petru-florea/Low-Frequency-Amplifier/Simulations/1.PNG

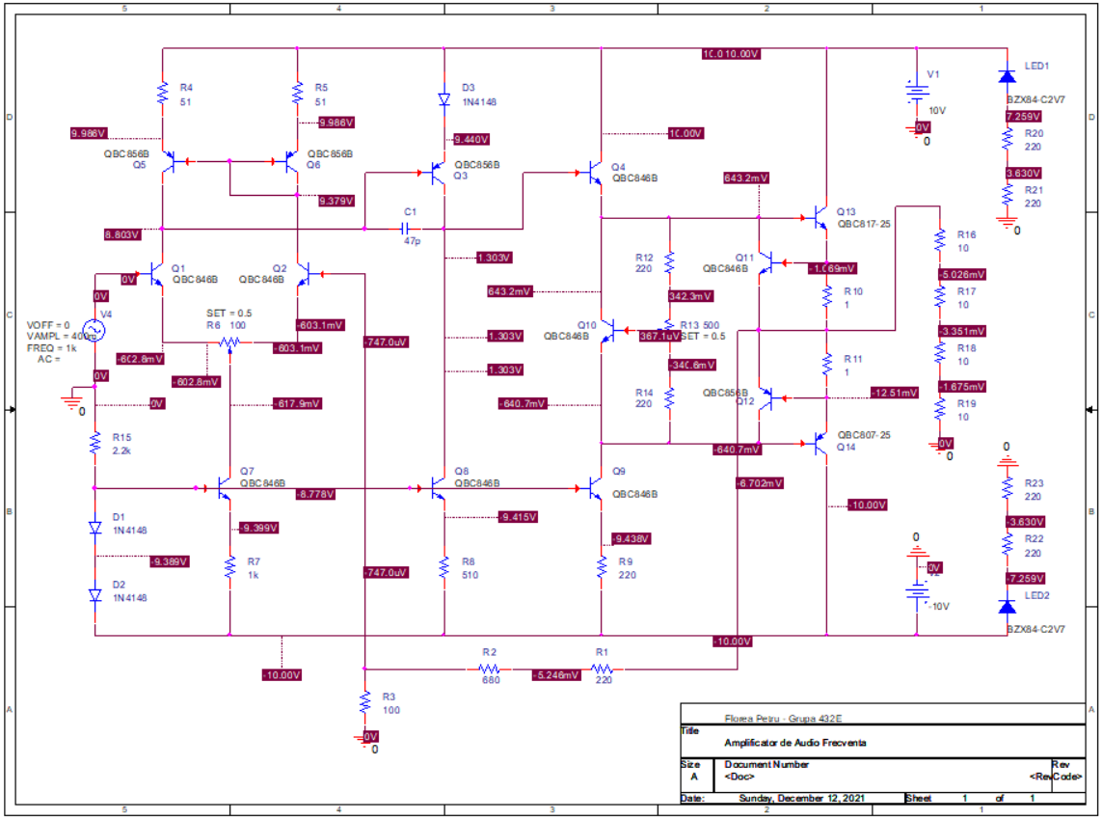
Simulations/1.PNG
