petru-florea/Low-Frequency-Amplifier/Simulations/2.PNG

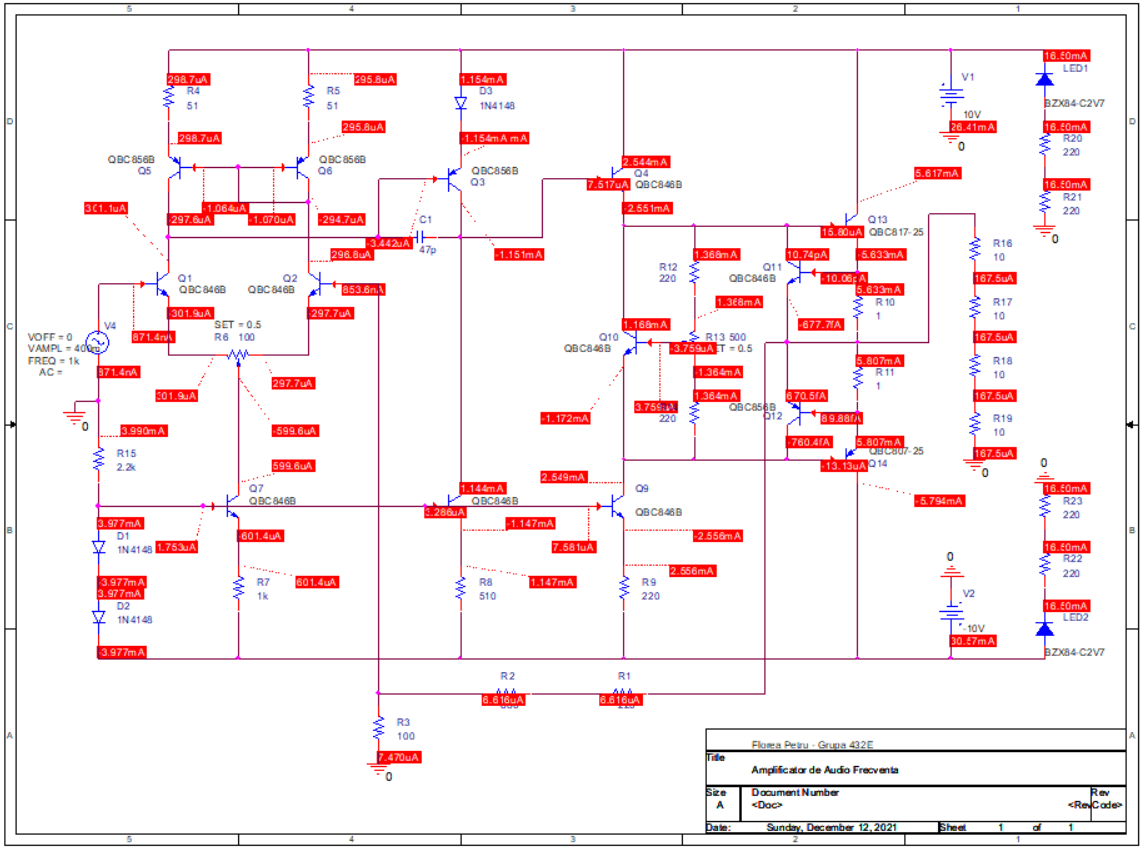
Simulations/2.PNG
