petru-florea/Low-Frequency-Amplifier/Simulations/3.PNG

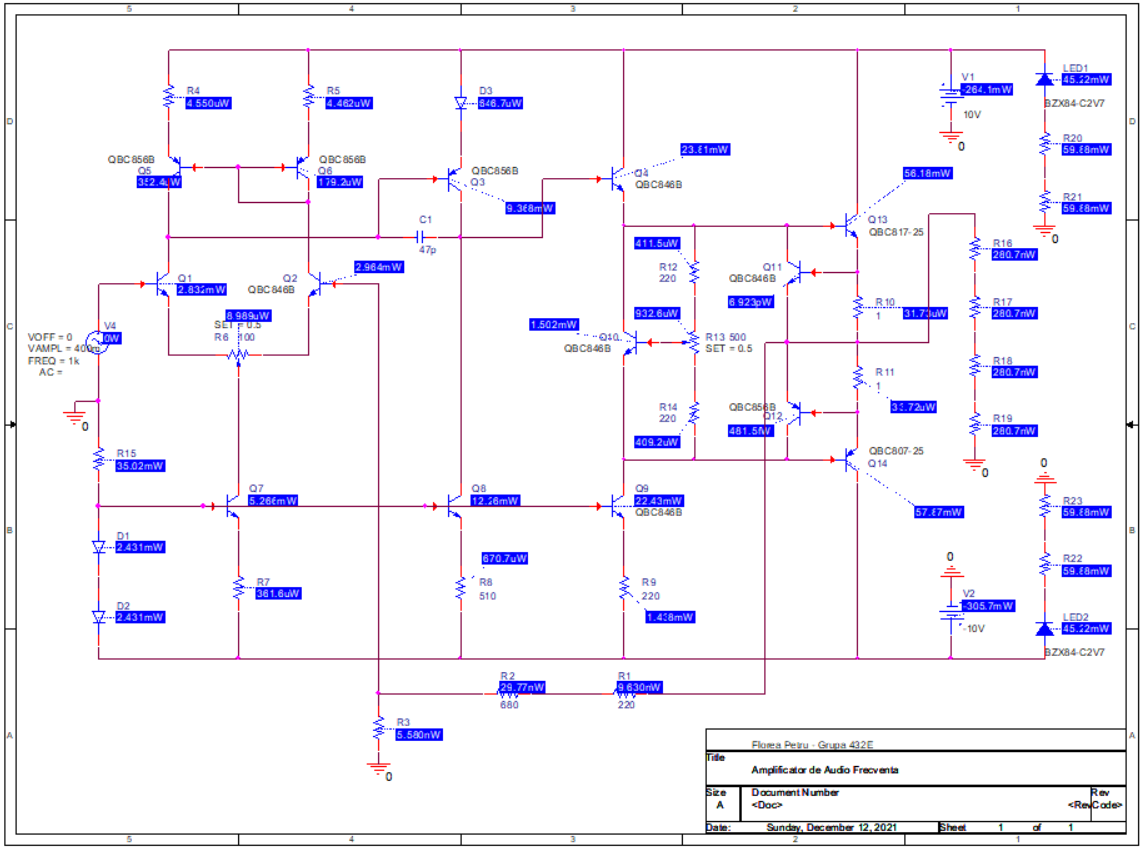
Simulations/3.PNG
