petru-florea/Low-Frequency-Amplifier/Simulations/4.JPG

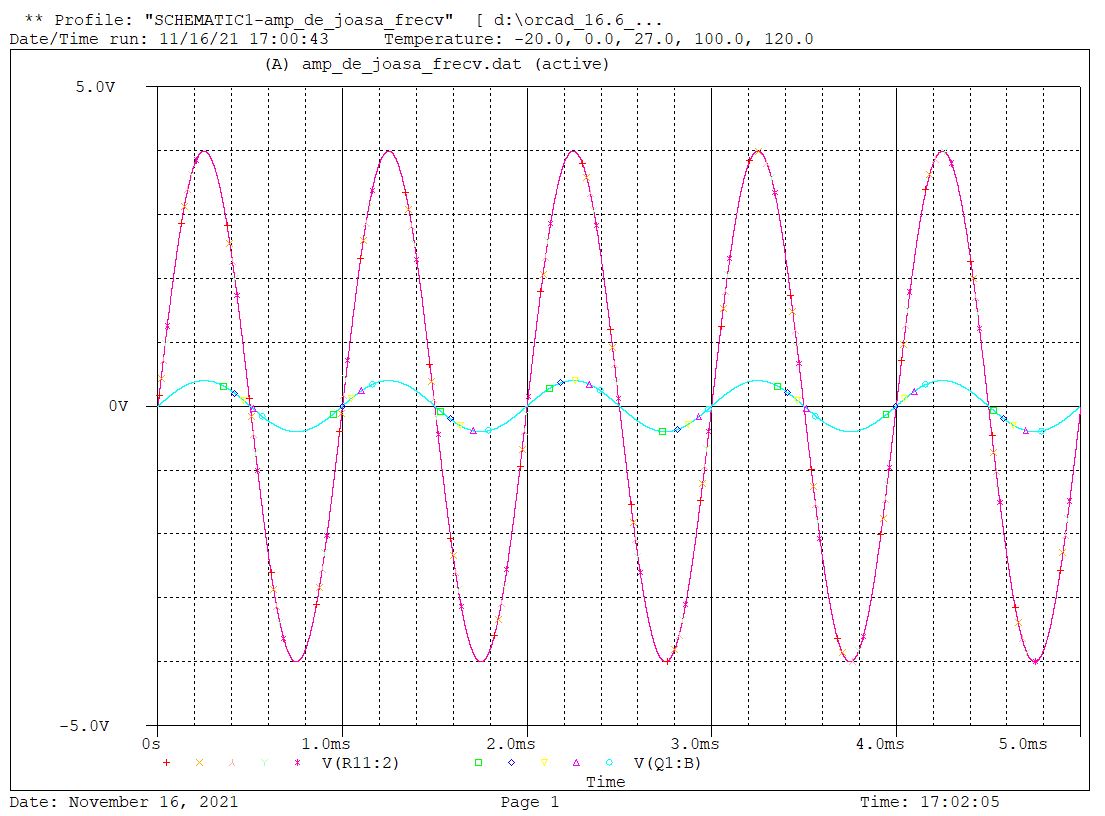
Simulations/4.JPG
