petru-florea/Low-Frequency-Amplifier/Simulations/5.JPG

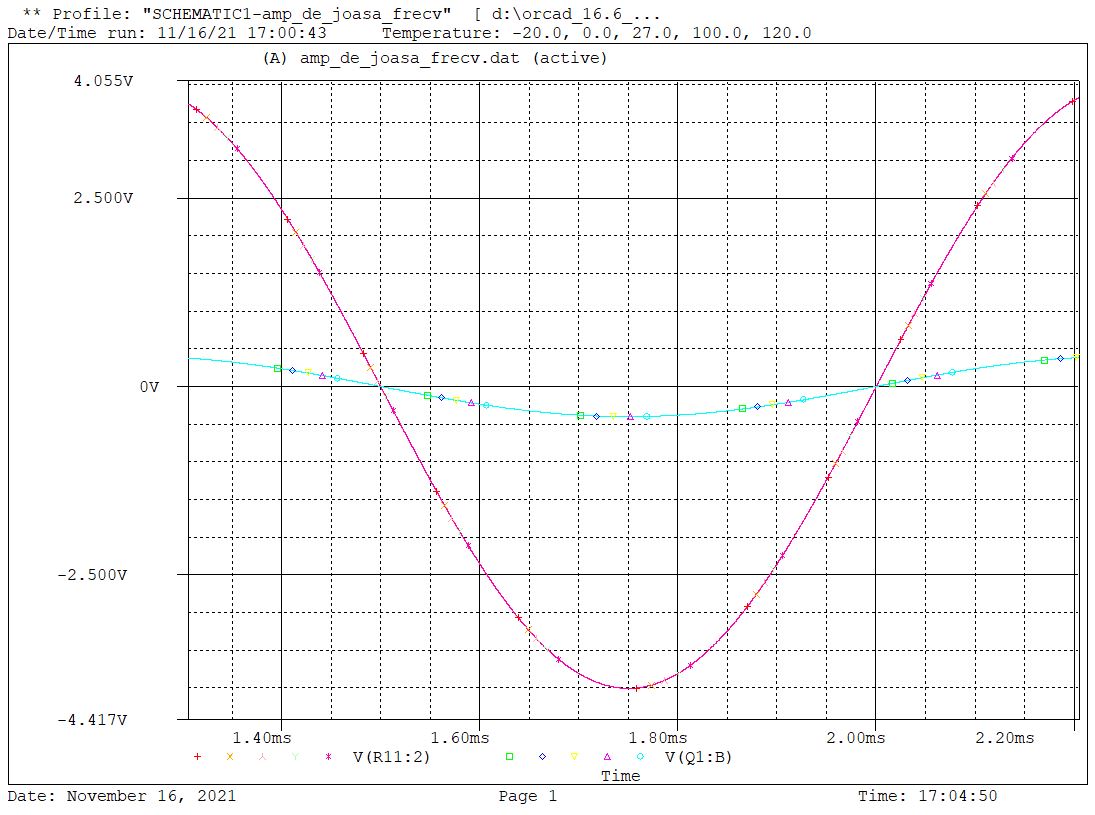
Simulations/5.JPG
