petru-florea/Low-Frequency-Amplifier/Simulations/6.JPG

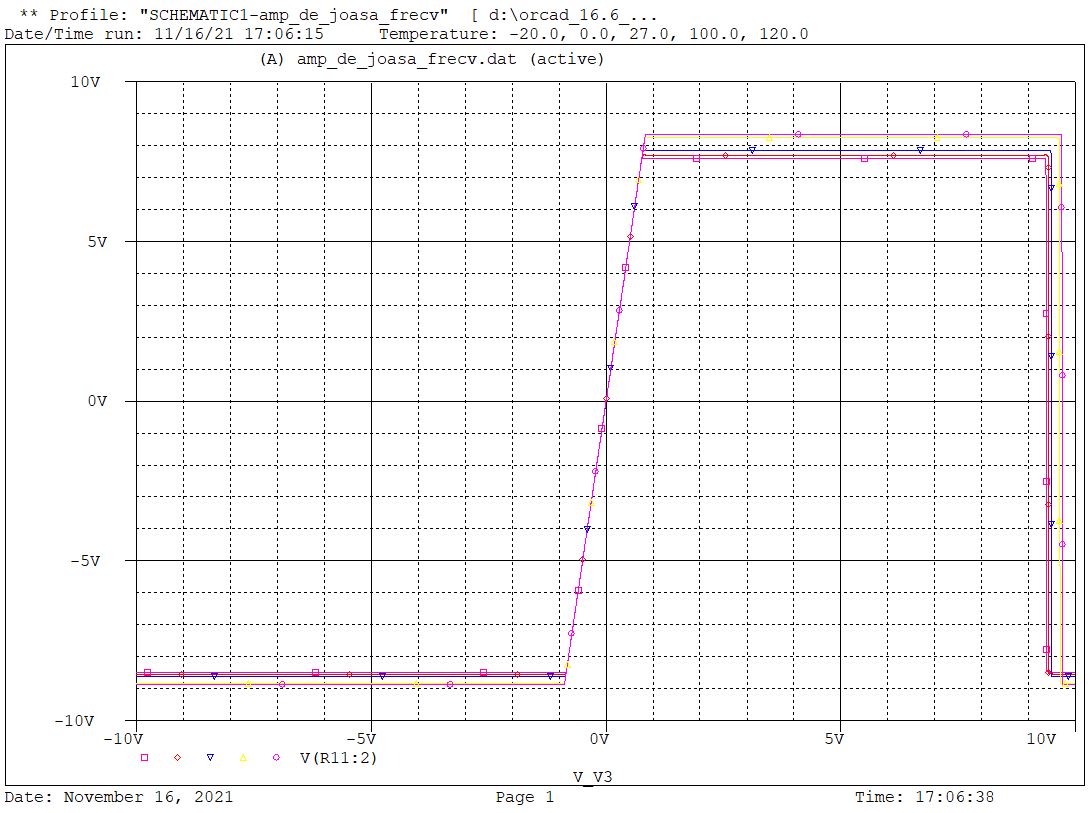
Simulations/6.JPG
