petru-florea/Low-Frequency-Amplifier/Simulations/7.JPG

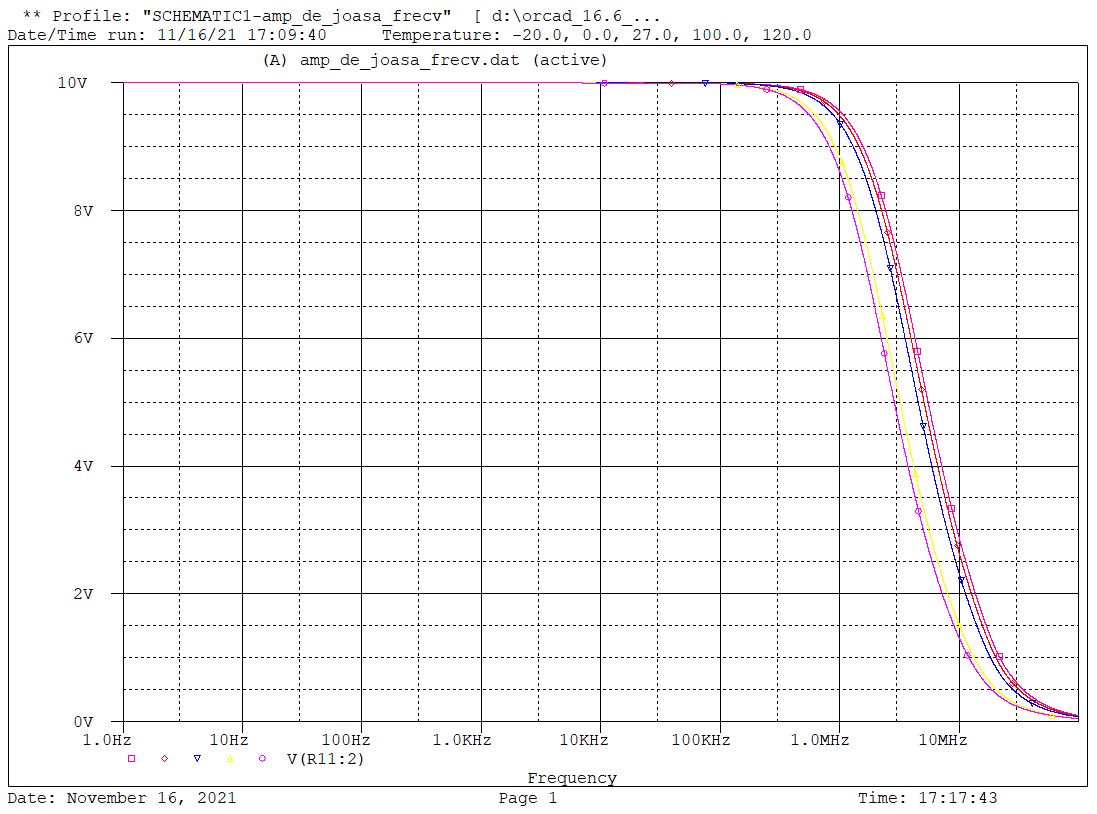
Simulations/7.JPG
