petru-florea/Low-Frequency-Amplifier/Simulations/8.JPG

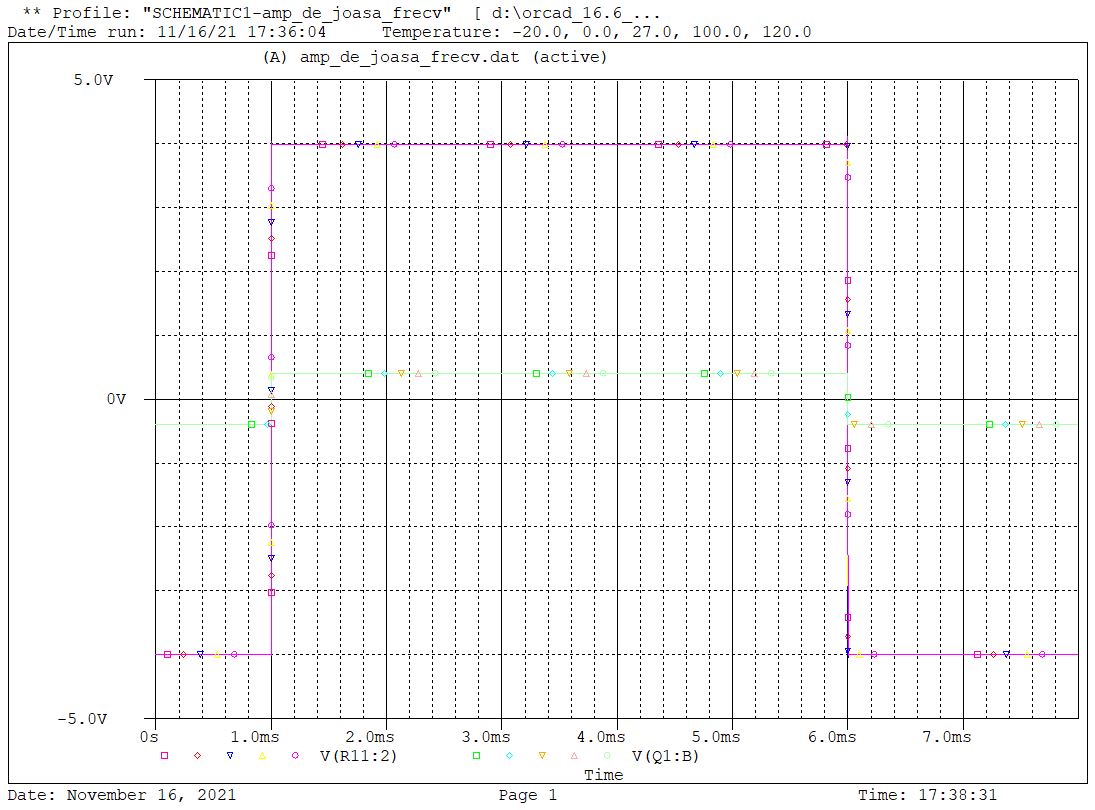
Simulations/8.JPG
