petru-florea/Low-Frequency-Amplifier/Simulations/9.JPG

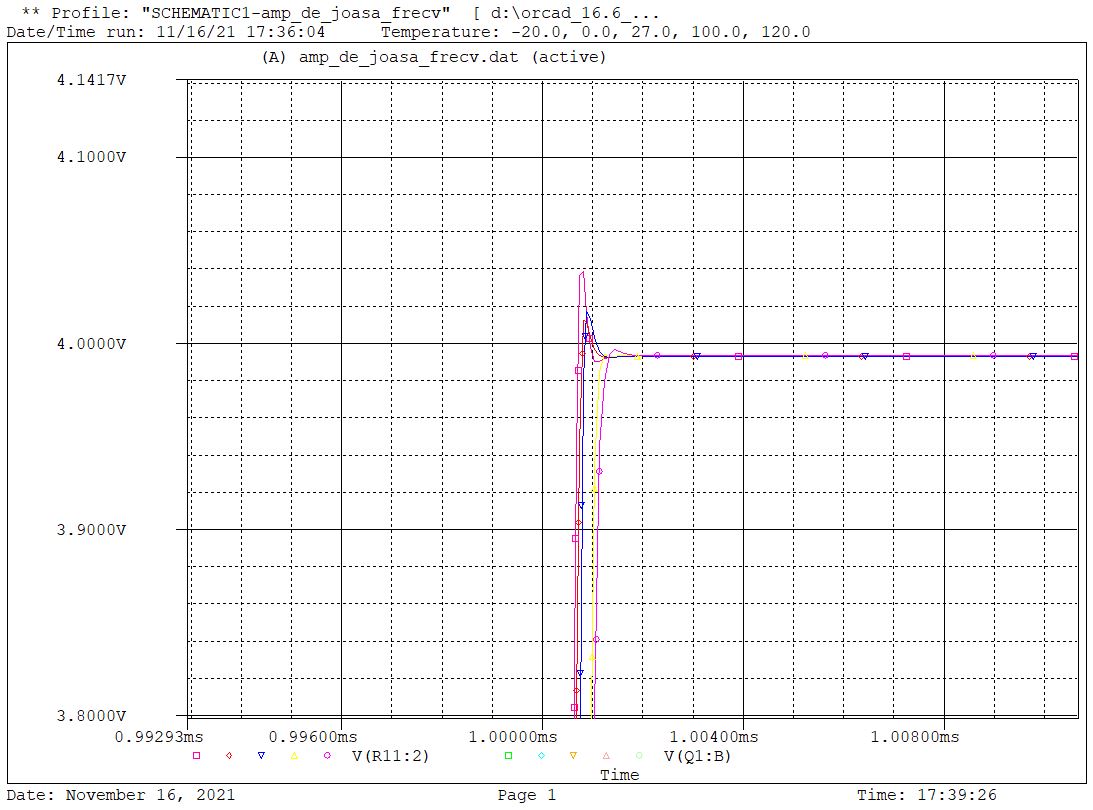
Simulations/9.JPG
