petru-florea/Low-Frequency-Amplifier/Simulations/10.JPG

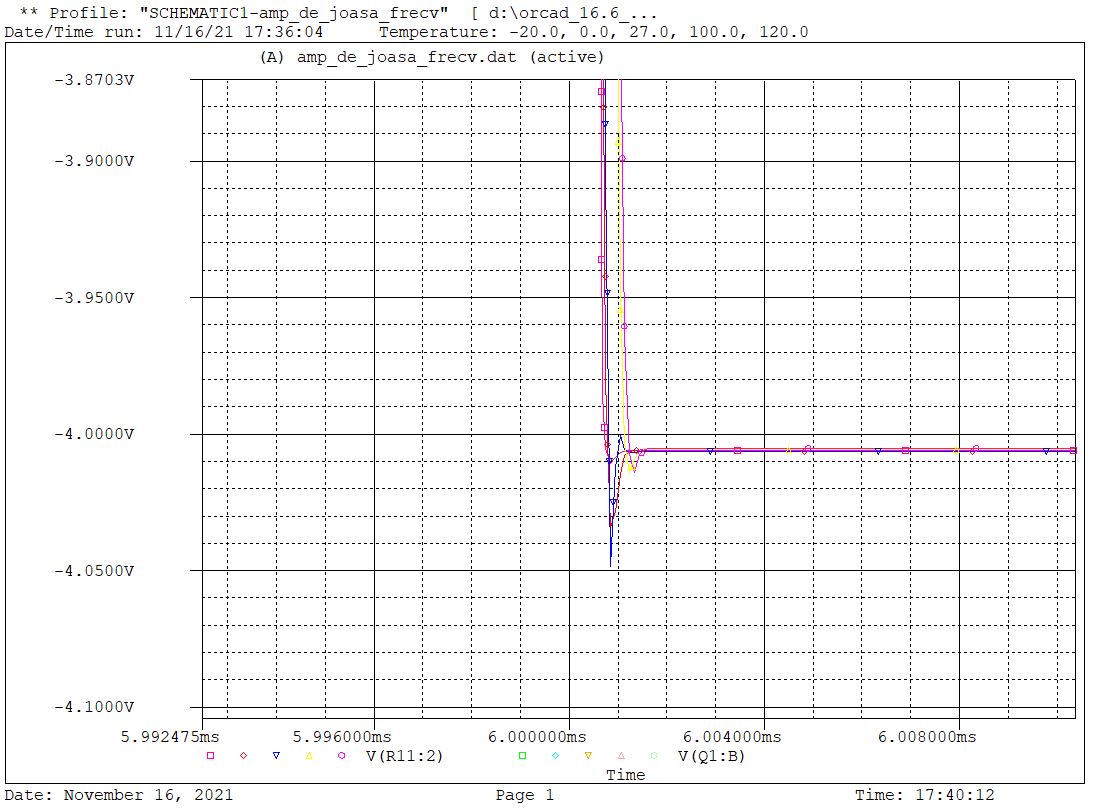
Simulations/10.JPG
