petru-florea/Low-Frequency-Amplifier/Simulations/11.JPG

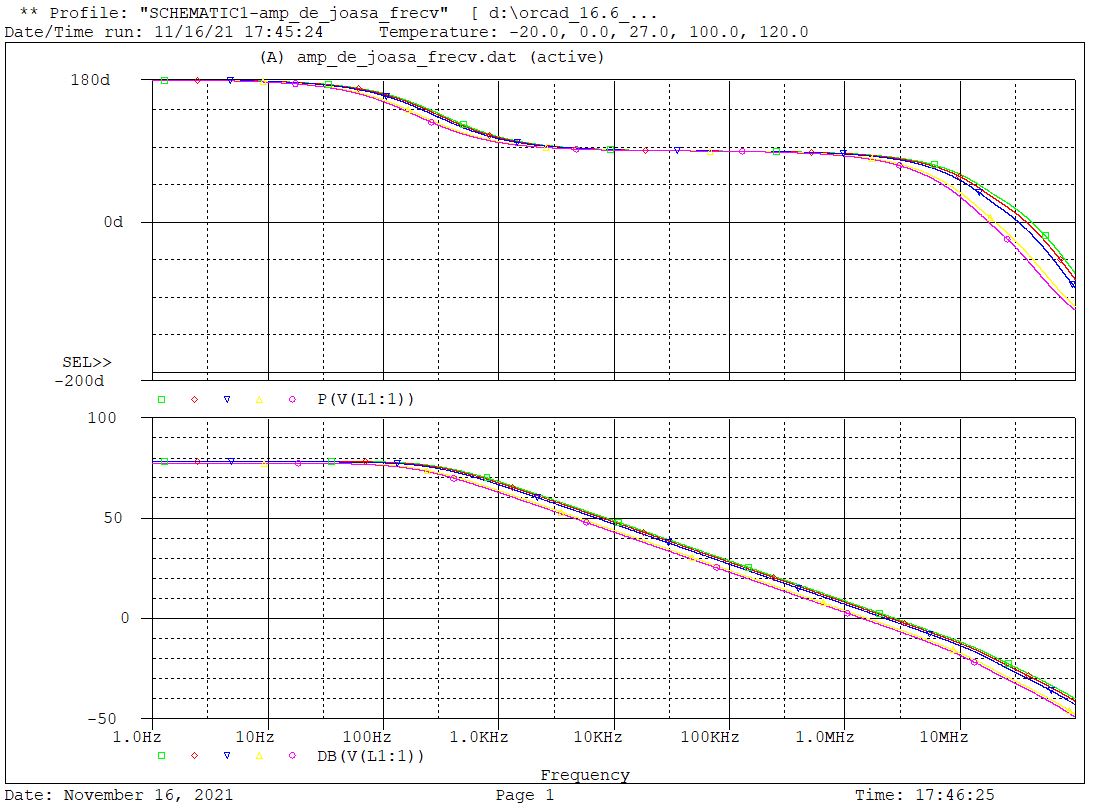
Simulations/11.JPG
