petru-florea/Low-Frequency-Amplifier/Simulations/Fourier.JPG

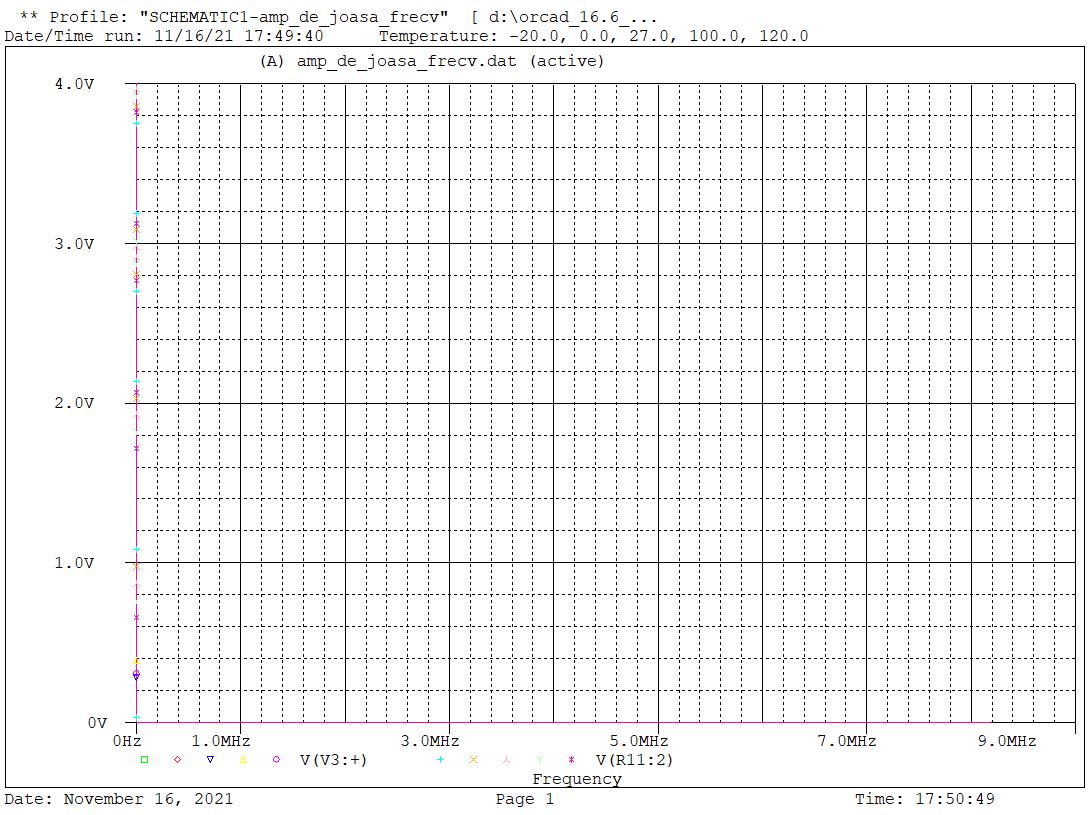
Simulations/Fourier.JPG
